cognitivegears/PiCoCo/docs/kicad-workflow.md

# KiCad Workflow — PiCoCo v2.3

What's in the repo right now, what you do with it in KiCad, and how
to verify the design is correct at each step.

Current schematic/PCB revision: **v2.3.1** — carrier for either a
Raspberry Pi Pico 2 or a Waveshare RP2350B-Plus-W (`PiCoCo:Pico-Carrier`
footprint/symbol, generated), U10–U13 all `SN74LVC245A` at 3.3 V, U15
replaced by a `74LVC00` (SOIC-14) wired NAND-NAND, JP2/JP3/JP4/JP5
solder jumpers, a populated-by-default sound stage to cart pin 35, no
`J_SWD` header and no mounting hole, fully routed with GND pours and an
8 mm stitching grid on both layers, and an order-ready JLCPCB fab
package under `fab/main/`.

**v2.3.1 (2026-09-18)**: bench measurement of a CoCo 3's cartridge
opening showed the module's USB-C port and the reserved HDMI corner
landed on or outside the case surface at the v2.3 board length, so the
outline grew 12 mm away from the fingers — 98 x 67.0 mm body + 10.16 mm
finger tongue, 77.16 mm overall (was 98 x 55 mm). Everything at or
above JP2's row (module, JP3, C10, TP1–6, keepouts, top-edge silk)
moved up with it. The same pass fixed several pre-order review items:
R7 100 k -> 10 k, R10 DNP, R3 populated, new R23/R25 pull-ups, the
sound stage's C15/R24 AC-coupling swap, JP3's default flipped to audio,
new JP4 autostart tie, TP8 and FID3 added, and the 100 kΩ/0 Ω LCSC
numbers updated. See spec §11 for the full list.

**v2.3.1 (2026-09-19)**, from the three quality reviews before the
first order: **JP5** (open, 3-pad) gives a Pico 2 a firmware-pulsed
`/CART` or `/NMI` over header pin 34, sharing the pin with JP3 — never
bridge both — and its Q4/R16/R18 stage is now populated (Q3/R15/R17
stay DNP, for `/NMI`); **J1** ("EXP (Plus-W)", DNP) breaks out the four
previously no-connect Plus-W pad-grid pins (GP35/43/44/45); **C16**
(10 µF) adds local +3V3 bulk at the buffer row; the sound stage's
R19/R20 dropped to 470 Ω and R21 to 1 kΩ (was 1 kΩ/1 kΩ/2.2 kΩ, which
loaded-network math showed gave only 0.63 V pk-pk / 9.1 kHz, not the
documented ~1 V / ~16 kHz); a GND via now sits at every decoupling cap
pad and IC GND pin plus an 8 mm stitching grid (`tools/gnd_stitch.py`);
`+5V`/`+3V3`/`VSYS_PICO` moved to a 0.5 mm Power netclass; and the
antenna keepout widened to x 151.3..158.0, y 32.7..55.7. See
`docs/hardware-design.md` §4.4a/§4.6/§6 and spec §11 for detail.

---

## 1. Current state of the files

| File | State |
|---|---|
| `PiCoCo/PiCoCo.kicad_sch` | **v2.3.1 schematic** — generated from `tools/gen_schematic.py`. v2.3 added JP2/JP3, Q3/Q4 (DNP), R15–R22, C12–C15, TP7, FID1/FID2; U10–U13 become `SN74LVC245A`; U15 becomes `74LVC00` (NAND-NAND); removed J_SWD, R6, JP1, C5, C11. v2.3.1 adds JP4, R23–R25, TP8, FID3, and rewires C15/R24 for AC coupling; flips JP3's default to audio; R7 100k->10k, R10 DNP, R3 populated. v2.3.1 adds JP5 (open), J1 (DNP "EXP (Plus-W)" header), C16 (local +3V3 bulk), populates Q4/R16/R18, and drops R19/R20 to 470 Ω and R21 to 1 kΩ. ERC-clean except the one known cosmetic `pin_to_pin` error (COCO-CART symbol library quirk, §2.2). |
| `PiCoCo/PiCoCo.kicad_sch.v1-backup` | Old schematic — preserved for reference. |
| `PiCoCo/PiCoCo.kicad_pcb` | **Fully routed and hand-finished** — GND pours on both layers, 0 DRC errors, 0 unconnected. Authoritative; KiCad GUI edits take precedence over any regenerator once you touch it directly. |
| `PiCoCo/PiCoCo.kicad_pcb.v1-backup` | PCB backup (original v1). |
| `PiCoCo/PiCoCo.kicad_pcb.pre-place` | Backup produced by `tools/place_pcb.py`'s last run. |
| `PiCoCo/PiCoCo.kicad_pro` | Design rules: Default netclass 0.20 mm track / 0.15 mm clearance, 0.8/0.4 mm vias; Power netclass (v2.3.1) 0.5 mm track for `+5V`/`+3V3`/`VSYS_PICO`, same clearance/via; floors: min track/clearance 0.127 mm, copper-to-edge 0.2 mm, hole clearance 0.25 mm. |
| `PiCoCo/fp-lib-table` and `sym-lib-table` | Use `${KIPRJMOD}/../libraries/` relative path. |
| `libraries/PiCoCo.pretty/COCO-CART-2.1X1.75.kicad_mod` | Finger pads trimmed to 1.30 mm from the edge (shared `FINGER_TRIM` regex, also used by `gen_breakout.py`). |
| `libraries/PiCoCo.pretty/Pico-Carrier.kicad_mod` | GENERATED by `gen_schematic.py`'s `write_carrier_footprint()` — the module footprint plus the 15-pad Plus-W grid and antenna courtyard. Do not hand-edit. |
| `libraries/PiCoCo.kicad_sym` | Local symbols: `Pico-Carrier`, `COCO-CART`, `74LVC00` — the first and third are GENERATED (`write_carrier_symbol()` / the inline 74LVC00 block in `gen_schematic.py`); `COCO-CART` is hand-authored. |
| `tools/gen_schematic.py` | Generator script. `python3 tools/gen_schematic.py` regenerates the schematic (and the two library files above) from the declarative placement + pin-map, then runs `check()` (assert-based self-check). |
| `tools/check_library.py` | Asserts the local symbols/footprints exist and are geometrically right (courtyard size, pad counts, etc). Stdlib only. |
| `tools/place_pcb.py` | Coarse footprint placement. Edits the first `(at X Y rot)` of each footprint, keeps pad/text angles consistent with the target rotation, and appends board-level EXTRAS (antenna/HDMI keepout zones, four track/via keepouts around U1's NPTH holes, silkscreen). Idempotent. **Destroys routing** if run against the routed board — see §"Routing". |
| `tools/autoroute.py` | Freerouting wrapper: DSN export → Freerouting → SES import → dangling-via/zero-length-segment cleanup → save. |
| `tools/grid_route.py` | A* router on pcbnew collision shapes, for the handful of nets Freerouting leaves unrouted. `--pair NET x1 y1 x2 y2` per net. |
| `tools/pour.py` | Adds/refreshes the GND pours on both copper layers and fills them. |
| `tools/gnd_stitch.py` | v2.3.1: drops a GND via at every decoupling cap's GND pad and every IC's GND pin, plus an 8 mm-pitch stitching grid across the buffer-row corridor, so the F.Cu/B.Cu GND pours stay tied together under the dense bus routing. Run after `finish_route`, before `pour.py`/`gnd_fix.py`. |
| `tools/gnd_fix.py` | Closes the GND net after pouring: routes stray GND clusters (pads/vias/pours not electrically joined); `--drc DRC_JSON` also fixes starved-thermal pads. |
| `tools/gen_fab.sh [pcb] [outdir]` | kicad-cli wrapper → Gerbers/drill/pos/BOM(+zip); defaults to the main board, output dir `fab/main/`. Also runs the JLCPCB BOM/CPL export + `tools/jlc_post.py` post-processing and the module-stencil Gerber export. |
| `tools/jlc_post.py` | Post-processes kicad-cli's raw BOM/CPL/paste-Gerber output into JLCPCB's expected formats; holds the per-footprint rotation-offset table. |
| `docs/hardware-design.md` | Full hardware design reference. |
| `docs/firmware-architecture.md` | Firmware architecture. |
| `fab/main/` | Main board fab package: Gerbers + drill (`PiCoCo-gerbers.zip`), JLC BOM/CPL (`PiCoCo-BOM-jlc.csv`, `PiCoCo-CPL-jlc.csv`), module stencil (`stencil-module/PiCoCo-stencil-module-F_Paste.gbr`), `READ-BEFORE-ORDERING.txt`. |
| `fab/` | `breakout/`, `cobbler/` — Gerber zips for the two breadboard boards. |

## 2. What to do in KiCad (step by step)

### 2.1 Open the project

1. Launch KiCad.
2. `File → Open Project…` → select `PiCoCo/PiCoCo.kicad_pro`.
3. Symbol and footprint libraries should resolve automatically thanks
   to the fixed `fp-lib-table` / `sym-lib-table` (they now use
   `${KIPRJMOD}`).

### 2.2 Review the schematic

1. Open Eeschema (`File → Open Schematic` or the schematic icon).
2. You should see all the v2.3 components placed in a grid. **It
   won't be pretty** — the generator places components on a grid
   with pins connected via global labels touching pin endpoints.
   Global labels are the wiring.
3. Run ERC: `Inspect → Electrical Rules Checker`. Expect **1 error**
   and 0 warnings. The error is the cosmetic `pin_to_pin` between
   P1 Pin 33 GND@1 and P1 Pin 34 GND@2 (both declared `power_output`
   in the `PiCoCo:COCO-CART` symbol — a library-level quirk). Ignore.
4. Optional — reshape the schematic for readability:
   - Rotate/move components so wires are visually obvious.
   - Convert clusters of global labels into net labels + short wires
     for nearby pins.
   - None of this affects the netlist; it's only for human reading.

### 2.3 Sync the PCB

1. Close the schematic editor first (KiCad holds file locks).
2. From the PCB editor: `Tools → Update PCB from Schematic…`
3. **Tick "Delete footprints with no corresponding symbol"** so old
   orphans get cleaned up automatically.
4. Regenerating from a pre-v2.3 board, expect this diff (already
   applied to the committed board — this is what Task 4 saw going
   from v2.2 to v2.3):
   - **U1** footprint changes from `RPi_Pico_SMD_TH` to `Pico-Carrier`
     (adds the 15-pad Plus-W grid, drops the SWD pads and pins 41-43).
   - **U10–U13** stay `SOIC-20W` but the symbol's value changes to
     `SN74LVC245A` on all four (U10 included — no more `SN74LVC8T245`).
   - **U15** footprint changes from `SC-70-6` to `SOIC-14` (`74LVC00`
     replaces `74LVC1G11`). KiCad removes the old footprint and adds
     the new one at origin.
   - **Removed**: `J_SWD`, R6, R13, R14, JP1, C5, C11 and their nets.
   - **Added**: JP2, JP3 (SMD solder jumpers), Q3/Q4 (SOT-23, DNP),
     R15–R22, C12–C15, TP7, FID1/FID2.
   - **Net renames**: `RESET_DBG` → `RESET_BUF`; new nets `SEL_N`,
     `OE_BUS_RAW` (U15's internal NAND-NAND node), `OE_FW`, `NMI_DRV`,
     `CART_DRV`, `PICO_P34`, `AUDIO_PWM`, `AUDIO_F1`, `AUDIO_F2`,
     `SND_CART`. Any hand-routed traces on surviving nets are
     preserved under their new names as long as the endpoints match.
5. Confirm. New footprints land at origin; the board as committed has
   already been placed and routed (see §"Routing") — don't run
   `place_pcb.py` again unless you intend a full reroute.

### 2.4 Place components

`tools/place_pcb.py`'s `PLACEMENT` dict is the source of truth for
coarse placement (row nearest the fingers: U10–U13 in signal order;
U14/D2/C1–C3/C12 near the +5V finger; Q2/R1 near /HALT; Q3/Q4 near
/NMI and /CART; JP2 next to U10 pin 19; the audio stage in a line
ending at the SND finger; JP3 next to the module's pin 34). Running it
against the routed board destroys routing — see §"Routing" below for
when you actually want to touch placement again.

### 2.5 Routing

See the dedicated **Routing** section below — the board was not routed
by hand track-by-track in the GUI; it went through an autoroute +
grid-route + pour pipeline, then a small amount of GUI hand-finishing.

## Routing

The routed board (`PiCoCo/PiCoCo.kicad_pcb`) came from this pipeline,
all four tools run under **KiCad's bundled Python**
(`/Applications/KiCad/KiCad.app/Contents/Frameworks/Python.framework/Versions/Current/bin/python3`)
because they drive the `pcbnew` API:

1. **`tools/autoroute.py BOARD [--passes N] [--out OUT] [--jar JAR]`**
   — exports a Specctra DSN, calls Freerouting, imports the resulting
   SES, and cleans up dangling vias / zero-length stub segments.
   Freerouting (`freerouting-2.4.1.jar`) is **untracked** and sits at
   the repo root — too large for git, and never add it. It needs
   **Java ≥ 25**: use `/opt/homebrew/opt/openjdk/bin/java`, not
   whatever's on `$PATH` (SDKMAN's JDK 21 fails with
   `UnsupportedClassVersionError`). It writes under `~/Library/Application
   Support/freerouting` and `~/Library/Logs/freerouting` and must run
   with the **Bash sandbox disabled** — run `autoroute.py` itself
   sandbox-disabled too, since it launches Freerouting as a
   subprocess (sandboxed, Freerouting hangs in a log4j retry loop).
2. **`tools/grid_route.py BOARD [--out OUT] --pair NET x1 y1 x2 y2 [--pair ...]`**
   — an A* router over `pcbnew`'s collision shapes, for the handful of
   nets Freerouting leaves unrouted (on this board: `SLENB_BUF`,
   `E_BUF`, `AUDIO_PWM`, `PICO_RUN`, `PICO_P34`, plus `A6_BUF` and
   `A11_BUF` after ripping up some GND stub tracks to free a corridor —
   GND is carried by the pours, so short GND stubs can be sacrificed
   and restored by re-pouring + stitching).
3. **`tools/pour.py BOARD [--out OUT]`** — adds/refreshes the GND pour
   on both F.Cu and B.Cu, board outline inset 0.3 mm, cut 1 mm above
   the edge fingers so the pour never reaches the gold-fingered area,
   and fills.
4. **`tools/gnd_fix.py BOARD [--out OUT] [--drc DRC_JSON]`** — links
   any stray GND clusters (pads, vias, pour islands) that the pour
   left electrically isolated. Pass a `kicad-cli pcb drc` JSON with
   `--drc` and it also fixes starved-thermal pads it finds in the
   report.

**Rip-up-and-reroute a net**: delete that net's existing tracks/vias
via the pcbnew API (a short one-off script, or in the GUI), then
re-run `grid_route.py --pair NET ...` for it, then `pour.py` +
`gnd_fix.py` to restore ground continuity, then DRC.

None of these four tools are a "regenerator" like `gen_schematic.py` —
they're aids for getting from an unrouted board to a routed one. **The
routed board in `PiCoCo/PiCoCo.kicad_pcb` is hand-finished and
authoritative**; the KiCad GUI is the source of truth once you've
routed in it, same as the existing rule for any manual PCB edit.
Re-running `place_pcb.py` on it will destroy the routing.

Two board properties worth knowing before you touch routing:

- `place_pcb.py`'s `EXTRAS` list writes four track/via keepout zones
  around U1's NPTH holes (the USB-connector legs) — DRC's
  `hole_clearance` rule isn't expressible in a DSN export, so
  Freerouting doesn't know to avoid them without this.
- **U11 pad 10 (GND)** has zone connection **"none"** rather than a
  thermal-relief spoke — it's tied to the GND pour by track + via
  instead, because the automated pour left it a starved thermal.

**Design rules actually in effect** (`PiCoCo.kicad_pro`): Default
netclass 0.20 mm track / 0.15 mm clearance, vias 0.8 mm pad / 0.4 mm
drill (a few 0.6/0.3 mm vias used for GND stitching); Power netclass
(v2.3.1) 0.5 mm track for `+5V`, `+3V3` and `VSYS_PICO`, same
clearance/via sizes. Design-rule floors: min track 0.127 mm, min
clearance 0.127 mm, copper-to-edge 0.2 mm, min hole clearance 0.25 mm.

**Final DRC** (`kicad-cli pcb drc --severity-all --schematic-parity`,
sandbox disabled): **0 errors, 0 unconnected, 0 schematic-parity
issues, 77 silkscreen warnings**. The warnings are reference
designators sitting over pads/board edge — not fab-blocking (JLCPCB
clips silkscreen that overlaps copper or the edge automatically) —
and are left as-is rather than chased down further.

## 2.6 Paste and stencils

**No module pads carry F.Paste** — neither the 40 through-hole/
castellation pads nor the 15-pad Plus-W grid. The module is never
factory-placed (it's soldered by hand, flat, with nothing under it),
so paste there would leave solder bumps under a part that can't be
reflowed in place. This means the production `F.Paste` Gerber
(`fab/main/PiCoCo-F_Paste.gtp`) has paste flashes only on the parts
JLCPCB's assembly line actually places.

`fab/main/stencil-module/PiCoCo-stencil-module-F_Paste.gbr` is a
**separate** stencil Gerber, produced from a temporary in-memory copy
of the board with U1's pads (castellations + grid) given an F.Paste
layer — nothing in the checked-in board or footprint changes. Cut this
as its own stencil if you're hand-soldering the module with hot air or
a paste syringe (mainly relevant for a Plus-W's 15 hidden pads; a
header-mounted Pico 2 doesn't need it at all).

## 2.7 JLCPCB files

`tools/gen_fab.sh` (via `tools/jlc_post.py`) produces, under
`fab/main/`:

- **`PiCoCo-BOM-jlc.csv`** — Comment, Designator, Footprint, LCSC Part
  #, MPN; grouped by value; DNP parts excluded.
- **`PiCoCo-CPL-jlc.csv`** — Designator, Mid X, Mid Y, Layer, Rotation.
  Rotation comes from `kicad-cli pcb export pos` plus a per-footprint
  offset table in `tools/jlc_post.py` (keyed by package substring:
  `SOIC-20W`, `SOIC-14`, `SOT-23`, `SOT-223`, `D_SMA`, `0805`,
  `CP_Elec`), checked against JLCPCB's placement preview on 2026-09-18
  for the v2.3.1 order (SOIC +270, SOT-23/SOT-223 +180, the rest 0; the
  comment above the table says why). After a footprint change, check the
  preview again; fix the table and rerun `gen_fab.sh` if it shows a part
  rotated wrong, then re-upload.
- Fiducials (`FID1`, `FID2`, `FID3`) currently still appear in the CPL —
  `kicad-cli`'s `--smd-only` flag treats the fiducial footprint as SMD
  at the PCB level. JLC's assembly process typically ignores fiducial
  refs in a CPL; left as-is rather than filtering it out.

## 3. Regenerating the schematic

If you want to change pin assignments or add components, edit
`tools/gen_schematic.py` (declarative — modify the `pin_nets`
dictionaries and the `SYMBOLS`/placement calls) and re‑run:

```bash
python3 tools/gen_schematic.py
```

This also rewrites `libraries/PiCoCo.kicad_sym` (the `Pico-Carrier` and
`74LVC00` symbols) and `libraries/PiCoCo.pretty/Pico-Carrier.kicad_mod`
as a side effect — never hand-edit those two files directly. The
script's `check()` runs automatically after `build()` and fails the
regeneration on a typo'd single-pin net, a banned `_B`/`_DBG` net name,
U10's A/B side ordering, U15's decode wiring, JP3's wiring, or a
missing `LCSC` on a non-DNP, in-BOM part.

Then:
1. **Close Eeschema first** (file‑lock races otherwise).
2. `python3 tools/gen_schematic.py` — overwrites the .kicad_sch.
3. Reopen Eeschema, run ERC. Expect the one known error, 0 warnings.
4. PCB editor: `Tools → Update PCB from Schematic`, **with
   "Delete footprints with no corresponding symbol" ticked**. This
   removes orphans from net renames.
5. If you added footprints, `python3 tools/place_pcb.py` will place
   only unsynced refs (it reports refs it can't find). **Do not** run
   it if you only touched electrical wiring on already-placed parts —
   it will re-place everything and discard routing.
6. Refill zones (`B` in pcbnew), rerun the Routing pipeline for any
   newly unrouted nets, run DRC, address any issues.

`tools/gen_breakout.py` (also under KiCad's bundled Python — it drives
the pcbnew API) imports from `gen_schematic.py` but does not use the
`Pico-Carrier` symbol/footprint; it must still run and reproduce an
identical breakout after a generator change (diff the generated
files against the committed `breakout/`).

## 3.1 Generating fab outputs

```bash
bash tools/gen_fab.sh
```

Needs the sandbox disabled (`mktemp -t` for the stencil temp copy is
blocked under the sandboxed shell). Produces Gerbers, drill, JLC
BOM/CPL, the module stencil, and a zip under `fab/main/`. The shipped
`fab/main/READ-BEFORE-ORDERING.txt` is the checklist for JLCPCB: ENIG
surface finish, hard gold fingers, 30° bevel, 1.6 mm board, the DNP
list, and a budget bare-board variant. **Do not skip it** — JLCPCB's
defaults will not gold-plate the cartridge fingers.

`tools/gen_fab.sh [pcb] [outdir]` also still works for the two
breakout boards (pass their path explicitly).

## 4. Common gotchas

- **Symbol library errors on open.** KiCad may complain that
  `PiCoCo:Pico-Carrier` or `PiCoCo:COCO-CART` is not in the global lib.
  That's fine — the symbols are embedded in the schematic's
  `lib_symbols` block, and the project-scoped `sym-lib-table`
  points at `${KIPRJMOD}/../libraries/`. If KiCad still complains,
  check `Preferences → Manage Symbol Libraries → Project Specific
  Libraries` shows a `PiCoCo` entry.
- **Footprint not found on "Update PCB from Schematic".** All
  footprints use standard KiCad libraries except the edge
  connector (`PiCoCo:COCO-CART-2.1X1.75`) and the module
  (`PiCoCo:Pico-Carrier`). Both come from the project's local
  `fp-lib-table`. If KiCad complains about any standard one
  (e.g. `Package_SO:SOIC-20W_7.5x12.8mm_P1.27mm`), check
  `Preferences → Manage Footprint Libraries → Global Libraries`
  and make sure the standard KiCad libraries are enabled.
- **`kicad-cli pcb drc` crashes with a Swift runtime error only inside
  the Claude Code sandbox** — run it with the sandbox disabled, and
  make sure `PiCoCo.kicad_pro` sits beside whatever `.kicad_pcb` you
  point it at, or it silently falls back to KiCad's stock design
  rules instead of this project's.
- **ERC warnings about `tri_state` pins.** Fixed in v2.3 by retyping
  the embedded `74LS245` copy's data pins to `passive` in the
  generator — if you see these warnings return after a generator
  change, check that retyping step wasn't reverted.

## 5. Bring-up plan

See `docs/pcb-bringup.md`: its phases 1-2 (visual, DMM, bench power with
no module) are the first sanity checks before fitting and flashing the
module. The firmware-side checks are `firmware/TEST_PLAN.md` sections F-K.
