cognitivegears/PiCoCo/docs/superpowers/plans/2026-09-08-firmware-pico-target.md

# PiCoCo Firmware Plan B: Pico Target Implementation Plan

> **For agentic workers:** REQUIRED SUB-SKILL: Use superpowers:subagent-driven-development (recommended) or superpowers:executing-plans to implement this plan task-by-task. Steps use checkbox (`- [ ]`) syntax for tracking.

**Goal:** Turn the host-tested core into a running RP2350 firmware: USB console, flash filesystem with USB drive export, the core1 bus loop, crash record and watchdog, ending with a runbook for the breadboard milestones.

**Architecture:** Same `picoco_core` sources as Plan A, now linked with `src/plat_pico.c` (platform functions), `src/usb/*` (TinyUSB composite: 2 CDC + MSC), `src/fs_flash.c` + `third_party/fatfs` (FAT on a 2.5 MB flash partition, also served over MSC in export mode), `src/bus/bus_core1.c` (the flash-free bus loop on core1), and `src/crash.c`. Core0 runs everything else in one main loop.

**Tech Stack:** Pico SDK 2.3.1 (`PICO_BOARD=pico2`), TinyUSB (bundled with the SDK), FatFS R0.15 (vendored), CMake + Ninja, arm-none-eabi-gcc, UF2 flashing over BOOTSEL.

**Spec:** `docs/superpowers/specs/2026-09-07-firmware-design.md` sections 4.1, 4.3, 4.4, 7, 8, 9 (crash record, isolation modes), 11 steps 4-5. Plan A's result is on `main` at 5381aee.

## Global Constraints

- Host build must keep passing after every task: `cmake -B build-host -G Ninja -DPICOCO_HOST=ON firmware && ninja -C build-host && ctest --test-dir build-host --output-on-failure` (9+ suites, ASan/UBSan, no warnings). Any change under `firmware/src/` that the host compiles is covered by this.
- Pico build: `cmake -B build-pico -G Ninja -DPICO_SDK_PATH=/Users/cognitivegears/projects/pico-sdk firmware && ninja -C build-pico` produces `build-pico/picoco.uf2`. Zero warnings in `firmware/` sources (SDK/TinyUSB/FatFS warnings are not ours).
- **core1 is flash-free.** Everything core1 executes is `BUS_HOT` or `static inline`; core1 never calls libc, logging, `plat_*`, or anything that might touch flash. The build defines `PICO_FLASH_ASSUME_CORE1_SAFE=1`. The Pico build uses `-O2` (SDK Release) so `ring.h` inlines are never emitted out of line.
- Only core1's read hooks write `bus_table[0x3F41]`/`[0x3F42]` (single-writer rule, spec section 5).
- Nothing in the core0 main loop blocks: USB writes drop when the host is not reading; flash writes are the one long operation and are bounded to one 4 KB erase per call.
- Flash partition: firmware in the first 1.5 MB (`0x000000..0x17FFFF`), FAT volume at `PICOCO_FS_OFFSET 0x180000`, size `PICOCO_FS_SIZE 0x280000` (2.5 MB), 512-byte logical sectors, 4 KB erase blocks.
- On-target verification steps need a Pico 2 on USB (no CoCo). If none is on hand, complete the build step, mark the on-target step "not run" in the report, and continue; do not fake output.
- Commit once per task, only files under `firmware/` (plus `docs/` when a task says so). Message `firmware: <task summary>`, ending with:
  `Co-Authored-By: Claude Fable 5.1 <noreply@anthropic.com>` and `Claude-Session: https://claude.ai/code/session_01RmFQ1HMPQxdKfGPZdaihVx`. Per-task commits were approved by the user for Plan A on 2026-09-07 and Plan B continues that.
- Keep it lazy: smallest code that meets the step. Mark deliberate shortcuts with `// ponytail:` naming the ceiling. No abstractions beyond those named here.
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
