cognitivegears/PiCoCo/docs/superpowers/specs/2026-10-01-rom-manager-design.md

# PiCoCo ROM manager: thin-client manager for every CoCo

Status: draft for review, 2026-10-01. Brainstormed with the user.
Supersedes the CoCo-side half of `2026-09-23-coco-manager-design.md` once
it ships; that spec's firmware half (virtual serial, console allowlist)
stays as it is.

## 1. Goals

1. One manager that is the board's front door on every CoCo, from a 16K
   CoCo 2 with plain Color BASIC to a CoCo 3. Prompted by the 2026-10-01
   bench CoCo 2 (26-3026, 16K, no Extended BASIC), which cannot start
   HDB-DOS and so cannot load today's `PICOCO.BIN`.
2. The 16K machine must not cap the manager. Today's `PICOCO.BIN` sits at
   its `$7B80` ceiling with no headroom on a 32K machine.
3. The board boots its saved default (HDB-DOS, a game ROM, or the
   manager). The manager comes up on request.
4. First version: launch ROM images, mount and create disk images, boot a
   disk (NitrOS-9 or an RS-DOS program), settings, WiFi, save.
   `PICOCO.BIN` is retired when it ships.

Non-goals for v1 are in section 10.
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
